strawberryskeleton/nuclear-reactor/schem/schem-nuclear-reactor.kicad_sch

## KiCad design schem/schem-nuclear-reactor.kicad_sch (2026-06-18)

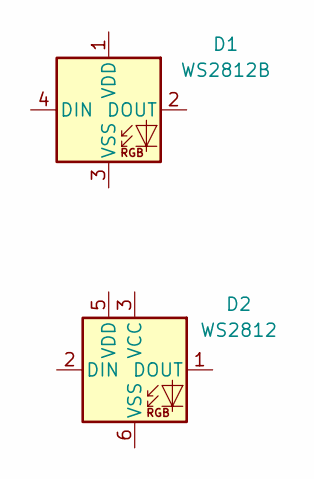
[picture p9: schematic schem-nuclear-reactor.kicad_sch]

Parts:
D1: WS2812B; LED_WS2812B_PLCC4_5.0x5.0mm_P3.2mm
D2: WS2812; LED_WS2812_PLCC6_5.0x5.0mm_P1.6mm
